Xmen097/USP/src/hardware/display_resources.h

#include <Adafruit_GFX.h>

/**
** 5x5 font
*
*
* Author Rob Jennings
*/

const uint8_t Font5x5FixedBitmaps[] PROGMEM = {
  0xE8, 0xA0, 0x5F, 0x5F, 0x50, 0xFA, 0xF5, 0xF0, 0xA5, 0x4A, 0x00, 0xEA,
  0xFA, 0xF0, 0x80, 0x6A, 0x40, 0x95, 0x80, 0xAA, 0x80, 0x5D, 0x00, 0xC0,
  0xE0, 0x80, 0x12, 0x48, 0x79, 0x99, 0xE0, 0xF8, 0xF1, 0xF8, 0xF0, 0xF1,
  0x71, 0xF0, 0x99, 0xF1, 0x10, 0xF8, 0xE1, 0xE0, 0xF8, 0xF9, 0xF0, 0xF1,
  0x24, 0x40, 0xF9, 0xF9, 0xF0, 0xF9, 0xF1, 0xF0, 0xA0, 0xB0, 0x2A, 0x22,
  0xE3, 0x80, 0x88, 0xA8, 0xE1, 0x60, 0x40, 0xFB, 0xB8, 0xF0, 0x69, 0xF9,
  0x90, 0xE9, 0xE9, 0xE0, 0x78, 0x88, 0x70, 0xE9, 0x99, 0xE0, 0xF8, 0xE8,
  0xF0, 0xF8, 0xE8, 0x80, 0x78, 0xB9, 0x60, 0x99, 0xF9, 0x90, 0xE9, 0x2E,
  0x00, 0x72, 0x2A, 0x60, 0x9A, 0xCA, 0x90, 0x88, 0x88, 0xF0, 0xFD, 0x6B,
  0x5A, 0x80, 0xF9, 0x99, 0x90, 0x69, 0x99, 0x60, 0xE9, 0xE8, 0x80, 0xF9,
  0x9B, 0xF0, 0xF9, 0xFA, 0x90, 0xF8, 0xF1, 0xF0, 0xE9, 0x24, 0x00, 0x99,
  0x99, 0xF0, 0x8C, 0x62, 0xA2, 0x00, 0xAD, 0x6B, 0x5F, 0x80, 0x8A, 0x88,
  0xA8, 0x80, 0x8C, 0x54, 0x42, 0x00, 0xF2, 0x48, 0xF0, 0xEA, 0xC0, 0x84,
  0x21, 0xD5, 0xC0, 0x54, 0xE0, 0x80, 0xE7, 0xF0, 0x93, 0x5E, 0x00, 0xF2,
  0x70, 0x25, 0xDE, 0x00, 0xFE, 0x70, 0x6B, 0xA4, 0xFC, 0xF0, 0x00, 0x93,
  0xDA, 0x00, 0xF0, 0x55, 0xC0, 0x97, 0x5A, 0x00, 0xAA, 0xC0, 0xFD, 0x63,
  0x10, 0xF6, 0xD0, 0x56, 0xA0, 0xFE, 0x40, 0xFC, 0x90, 0xF2, 0x40, 0xF1,
  0xF0, 0x5D, 0x24, 0x00, 0xB6, 0xF0, 0xB6, 0xA0, 0x8C, 0x6B, 0xF0, 0x96,
  0x69, 0xBD, 0x20, 0x00, 0xF2, 0x4F, 0x2B, 0x22, 0x00, 0xF8, 0x89, 0xA8,
  0xED, 0xC0
};

const GFXglyph Font5x5FixedGlyphs[] PROGMEM = {
  {     0,   0,   0,   3,    0,    1 }   // ' '
 ,{     0,   1,   5,   2,    0,   -4 }   // '!'
 ,{     1,   3,   1,   4,    0,   -4 }   // '"'
 ,{     2,   4,   5,   5,    0,   -4 }   // '#'
 ,{     5,   4,   5,   5,    0,   -4 }   // '$'
 ,{     8,   3,   5,   4,    0,   -4 }   // '%'
 ,{    11,   4,   5,   5,    0,   -4 }   // '&'
 ,{    14,   1,   1,   2,    0,   -4 }   // '''
 ,{    15,   2,   5,   3,    0,   -4 }   // '('
 ,{    17,   2,   5,   3,    0,   -4 }   // ')'
 ,{    19,   3,   3,   4,    0,   -3 }   // '*'
 ,{    21,   3,   3,   4,    0,   -3 }   // '+'
 ,{    23,   1,   2,   2,    0,   -1 }   // ','
 ,{    24,   3,   1,   4,    0,   -2 }   // '-'
 ,{    25,   1,   1,   2,    0,    0 }   // '.'
 ,{    26,   4,   4,   5,    0,   -3 }   // '/'
 ,{    28,   4,   5,   5,    0,   -4 }   // '0'
 ,{    31,   1,   5,   2,    0,   -4 }   // '1'
 ,{    32,   4,   5,   5,    0,   -4 }   // '2'
 ,{    35,   4,   5,   5,    0,   -4 }   // '3'
 ,{    38,   4,   5,   5,    0,   -4 }   // '4'
 ,{    41,   4,   5,   5,    0,   -4 }   // '5'
 ,{    44,   4,   5,   5,    0,   -4 }   // '6'
 ,{    47,   4,   5,   5,    0,   -4 }   // '7'
 ,{    50,   4,   5,   5,    0,   -4 }   // '8'
 ,{    53,   4,   5,   5,    0,   -4 }   // '9'
 ,{    56,   1,   3,   2,    0,   -3 }   // ':'
 ,{    57,   1,   4,   2,    0,   -3 }   // ';'
 ,{    58,   3,   5,   4,    0,   -4 }   // '<'
 ,{    60,   3,   3,   4,    0,   -3 }   // '='
 ,{    62,   3,   5,   4,    0,   -4 }   // '>'
 ,{    64,   4,   5,   5,    0,   -4 }   // '?'
 ,{    67,   4,   5,   5,    0,   -4 }   // '@'
 ,{    70,   4,   5,   5,    0,   -4 }   // 'A'
 ,{    73,   4,   5,   5,    0,   -4 }   // 'B'
 ,{    76,   4,   5,   5,    0,   -4 }   // 'C'
 ,{    79,   4,   5,   5,    0,   -4 }   // 'D'
 ,{    82,   4,   5,   5,    0,   -4 }   // 'E'
 ,{    85,   4,   5,   5,    0,   -4 }   // 'F'
 ,{    88,   4,   5,   5,    0,   -4 }   // 'G'
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
};

const GFXfont Font5x5Fixed PROGMEM = {
  (uint8_t  *)Font5x5FixedBitmaps,
  (GFXglyph *)Font5x5FixedGlyphs,
  0x20, 0x7E, 5 };

  /**
** 4x5 font
*
* Author Rob Jennings
*/

const uint8_t Font4x5FixedBitmaps[] PROGMEM = {
  0xE8, 0xA0, 0x5F, 0x5F, 0x50, 0xFA, 0xF5, 0xF0, 0xA5, 0x4A, 0x00, 0xEA,
  0xFA, 0xF0, 0x80, 0x6A, 0x40, 0x95, 0x80, 0xAA, 0x80, 0x5D, 0x00, 0xC0,
  0xE0, 0x80, 0x12, 0x48, 0x76, 0xDC, 0x00, 0xF8, 0xE7, 0xCE, 0x00, 0xE5,
  0x9E, 0x00, 0xB7, 0x92, 0x00, 0xF3, 0x1C, 0x00, 0xF3, 0xDE, 0x00, 0xE5,
  0x48, 0x00, 0xF7, 0xDE, 0x00, 0xF7, 0x9E, 0x00, 0xA0, 0xB0, 0x2A, 0x22,
  0xE3, 0x80, 0x88, 0xA8, 0xC5, 0x04, 0x00, 0xFB, 0xB8, 0xF0, 0x57, 0xDA,
  0x00, 0xD7, 0x5C, 0x00, 0x72, 0x46, 0x00, 0xD6, 0xDC, 0x00, 0xF3, 0x4E,
  0x00, 0xF3, 0x48, 0x00, 0x78, 0xB9, 0x60, 0xB7, 0xDA, 0x00, 0xE9, 0x2E,
  0x00, 0x24, 0xD4, 0x00, 0xB7, 0x5A, 0x00, 0x92, 0x4E, 0x00, 0xFF, 0x99,
  0x90, 0xF6, 0xDA, 0x00, 0x56, 0xD4, 0x00, 0xD7, 0x48, 0x00, 0xF9, 0x9B,
  0xF0, 0xF7, 0xEA, 0x00, 0xF3, 0x9E, 0x00, 0xE9, 0x24, 0x00, 0xB6, 0xDE,
  0x00, 0xB6, 0xD4, 0x00, 0x99, 0x9F, 0xF0, 0xB5, 0x5A, 0x00, 0xB5, 0x24,
  0x00, 0xE5, 0x4E, 0x00, 0xEA, 0xC0, 0x84, 0x21, 0xD5, 0xC0, 0x54, 0xE0,
  0x80, 0xE7, 0xF0, 0x93, 0x5E, 0x00, 0xF2, 0x70, 0x25, 0xDE, 0x00, 0xFE,
  0x70, 0x6B, 0xA4, 0xFC, 0xF0, 0x00, 0x93, 0xDA, 0x00, 0xF0, 0x55, 0xC0,
  0x97, 0x5A, 0x00, 0xAA, 0xC0, 0xFF, 0x99, 0xF6, 0xD0, 0x56, 0xA0, 0xFE,
  0x40, 0xFC, 0x90, 0xF2, 0x40, 0xF1, 0xF0, 0x5D, 0x24, 0x00, 0xB6, 0xF0,
  0xB6, 0xA0, 0x99, 0xFF, 0x96, 0x69, 0xBD, 0x20, 0x00, 0xE5, 0x70, 0x2B,
  0x22, 0x00, 0xF8, 0x89, 0xA8, 0xCC, 0x00
};

const GFXglyph Font4x5FixedGlyphs[] PROGMEM = {
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
};

const unsigned char debug_spliter [] PROGMEM = {
	0x04, 0x10, 0x41, 0x04, 0x10, 0x41, 0x04, 0x10, 0x41, 0x04, 0x10, 0x41, 0x04, 0x10, 0x41, 0x00, 
	0x04, 0x10, 0x41, 0x04, 0x10, 0x41, 0x04, 0x10, 0x41, 0x04, 0x10, 0x41, 0x04, 0x10, 0x41, 0x00
};
